adamf/click-clack/kicad/click-clack.kicad_sch

## KiCad design kicad/click-clack.kicad_sch (2026-06-29)

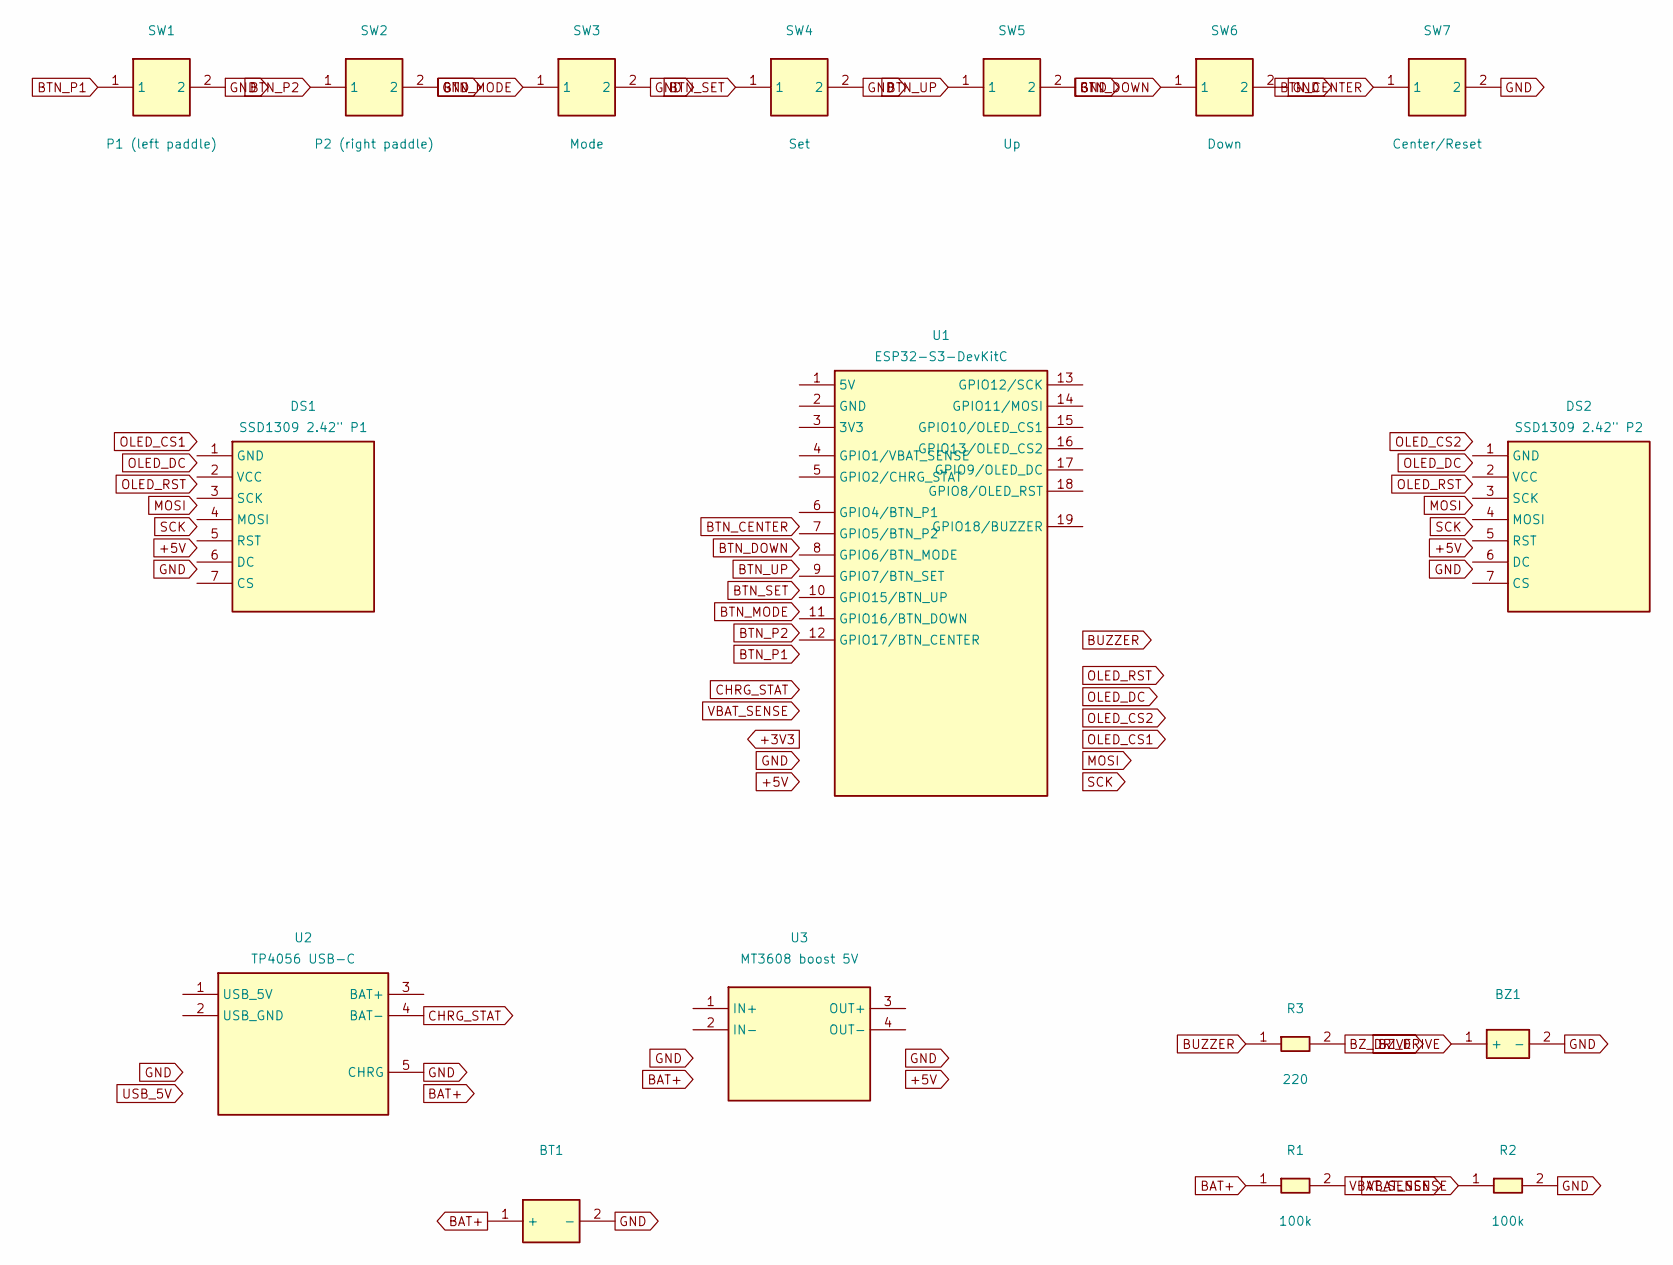
[picture p7: schematic click-clack.kicad_sch]

Parts:
BT1: (no value)
BZ1: (no value)
DS1: SSD1309 2.42" P1
DS2: SSD1309 2.42" P2
R1, R2: 100k
R3: 220
SW1: P1 (left paddle)
SW2: P2 (right paddle)
SW3: Mode
SW4: Set
SW5: Up
SW6: Down
SW7: Center/Reset
U1: ESP32-S3-DevKitC
U2: TP4056 USB-C
U3: MT3608 boost 5V

Connections:
BAT+: BT1.1 (+), R1.1
BTN_CENTER: SW7.1
BTN_DOWN: SW6.1
BTN_MODE: SW3.1
BTN_P1: SW1.1
BTN_P2: SW2.1
BTN_SET: SW4.1
BTN_UP: SW5.1
BUZZER: R3.1
BZ_DRIVE: BZ1.1 (+), R3.2
CHRG_STAT: U2.4 (BAT-)
GND: BT1.2 (-), BZ1.2 (-), R2.2, SW1.2, SW2.2, SW3.2, SW4.2, SW5.2, SW6.2, SW7.2, U2.5 (CHRG)
VBAT_SENSE: R1.2, R2.1
